pablobarron7/SmartBat_Capstone_2022/MCU Design/PCBTest.png

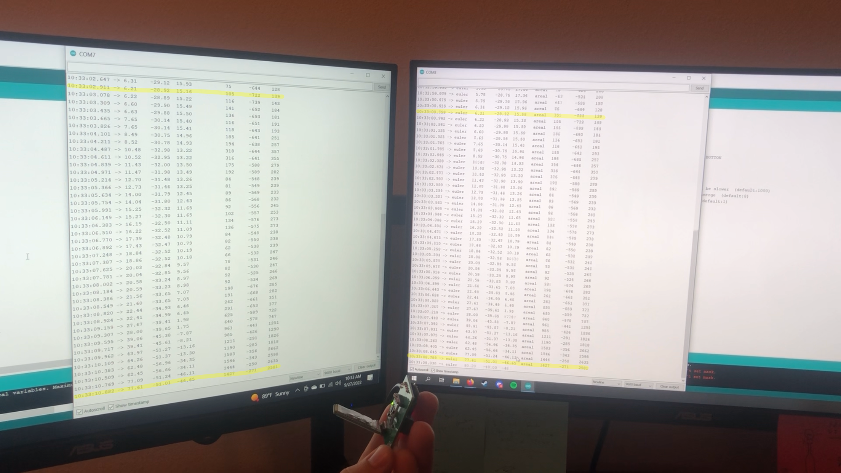
MCU Design/PCBTest.png
