pablobarron7/SmartBat_Capstone_2022/ML_EC2_Output/location3output.jpg

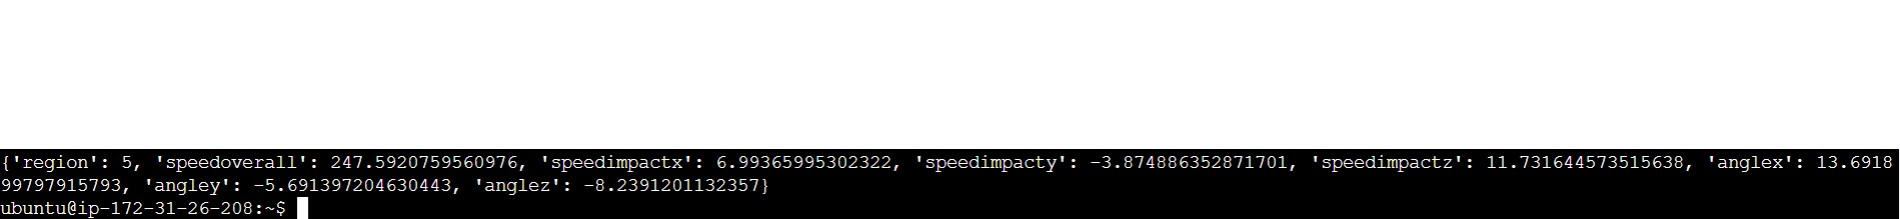
ML_EC2_Output/location3output.jpg
