pablobarron7/SmartBat_Capstone_2022/Bluetooth Validation/BTDistanceTest.PNG

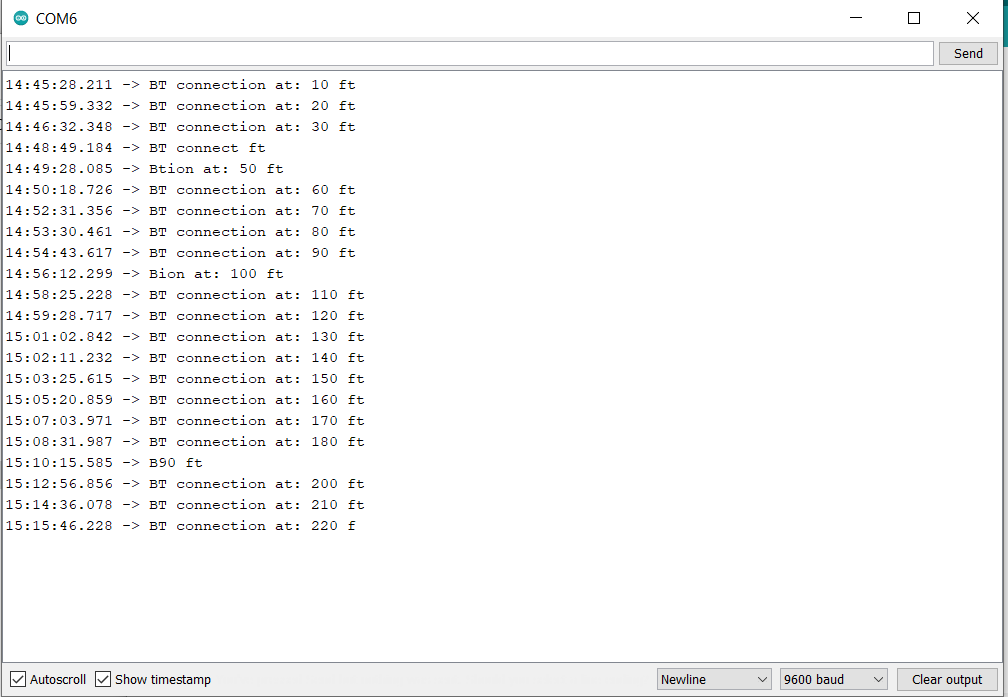
Bluetooth Validation/BTDistanceTest.PNG
