pablobarron7/SmartBat_Capstone_2022/Bluetooth Validation/Orignal Test/AppSideBTTest.PNG

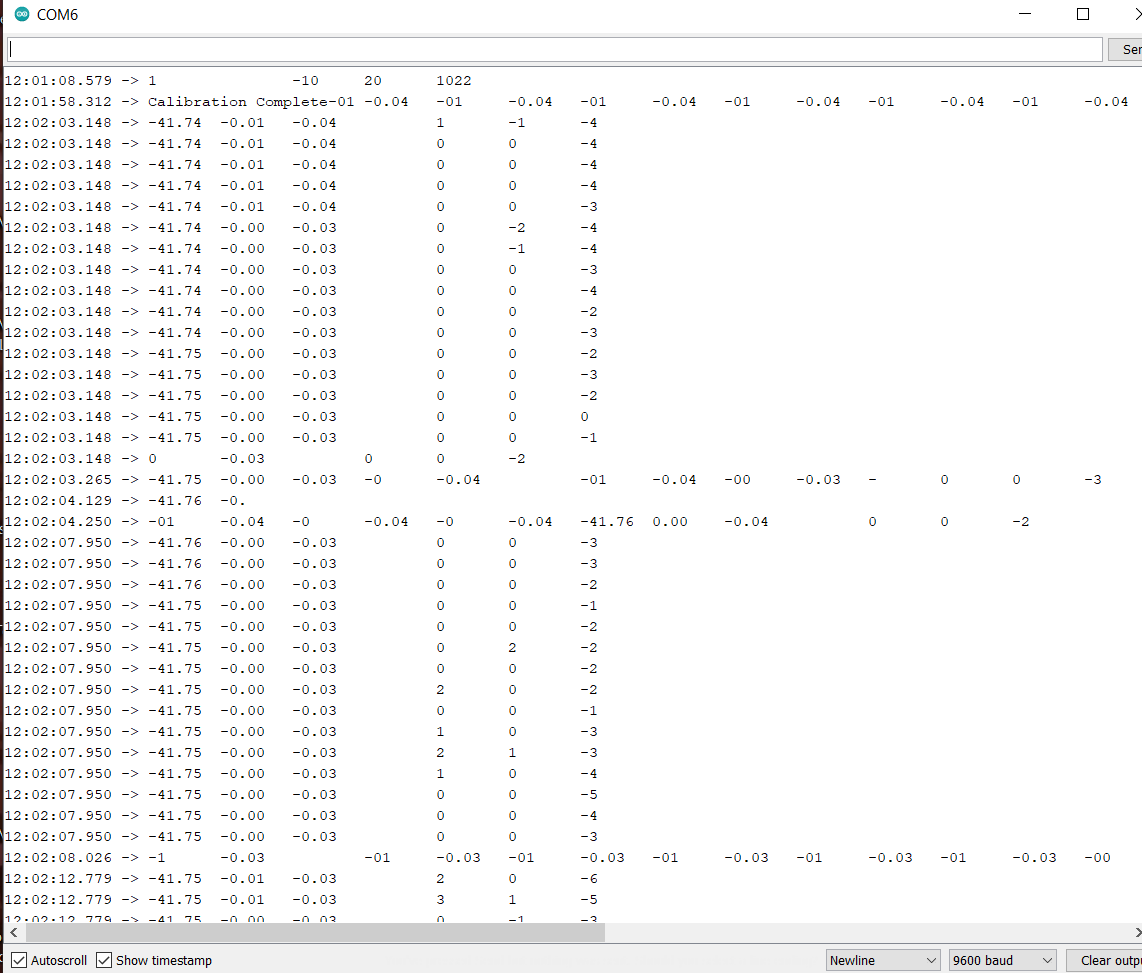
Bluetooth Validation/Orignal Test/AppSideBTTest.PNG
