pablobarron7/SmartBat_Capstone_2022/IMU Validation Plots/AccelerationMagPlot.png

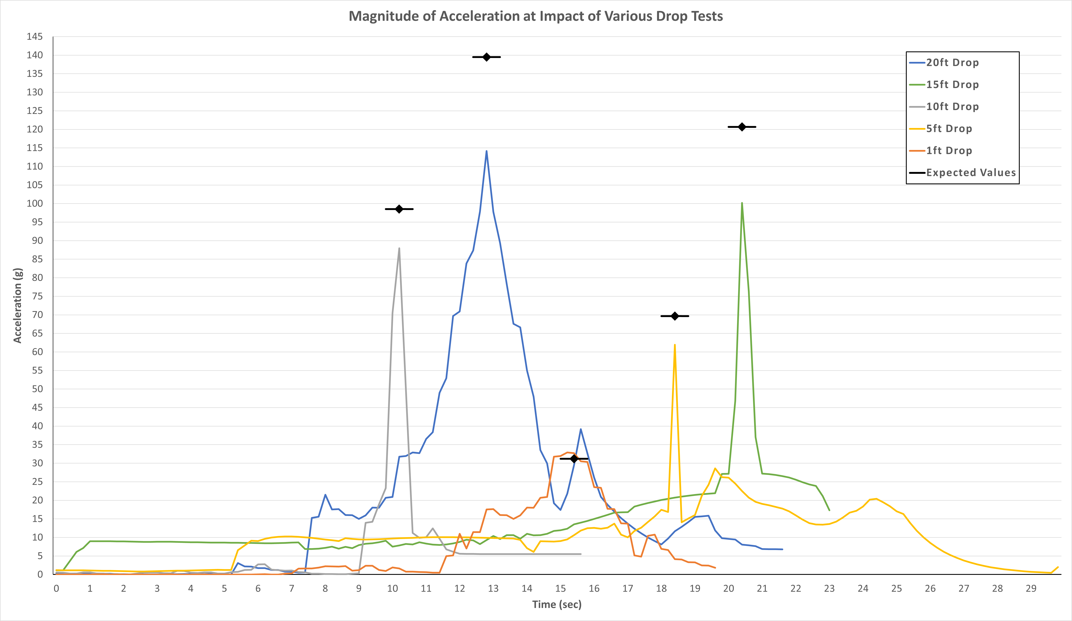
IMU Validation Plots/AccelerationMagPlot.png
