pablobarron7/SmartBat_Capstone_2022/IMU Validation Plots/GyroXAxis0to90.png

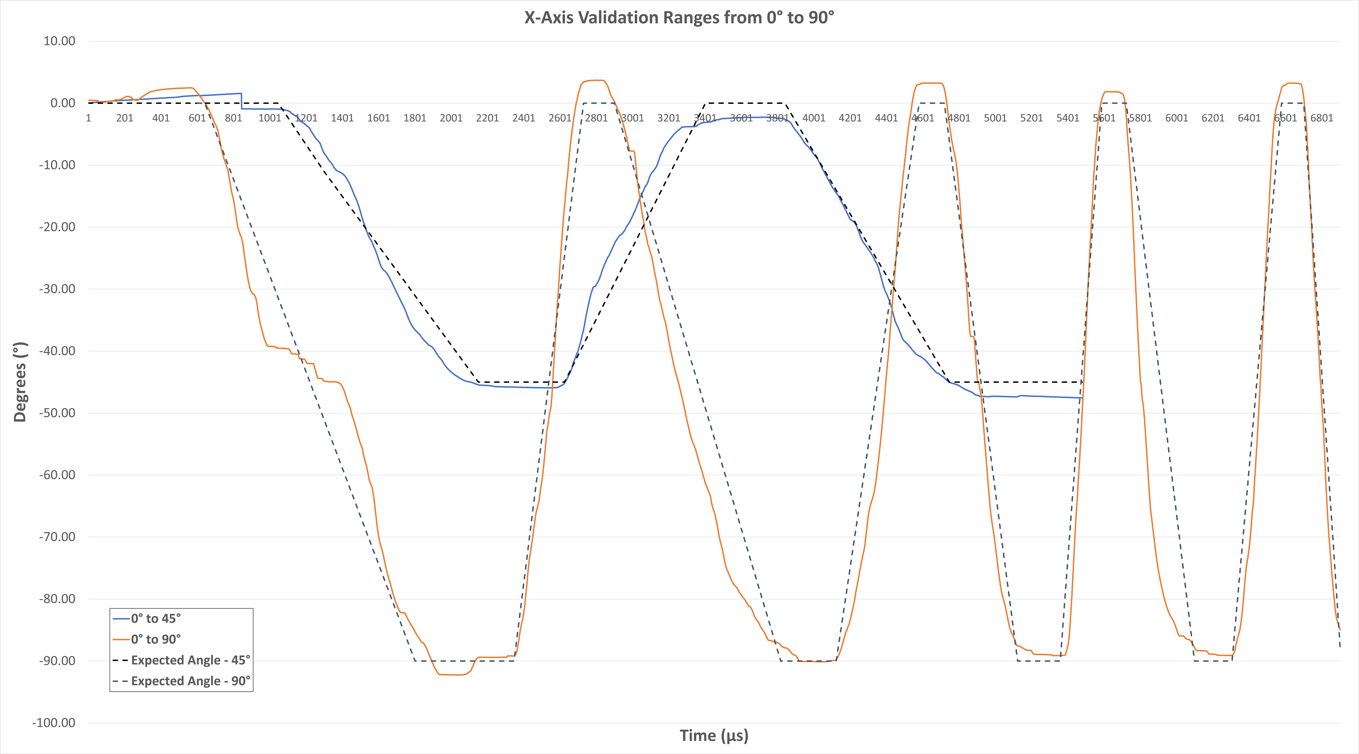
IMU Validation Plots/GyroXAxis0to90.png
