pablobarron7/SmartBat_Capstone_2022/IMU Validation Plots/GyroXAxis135to180.png

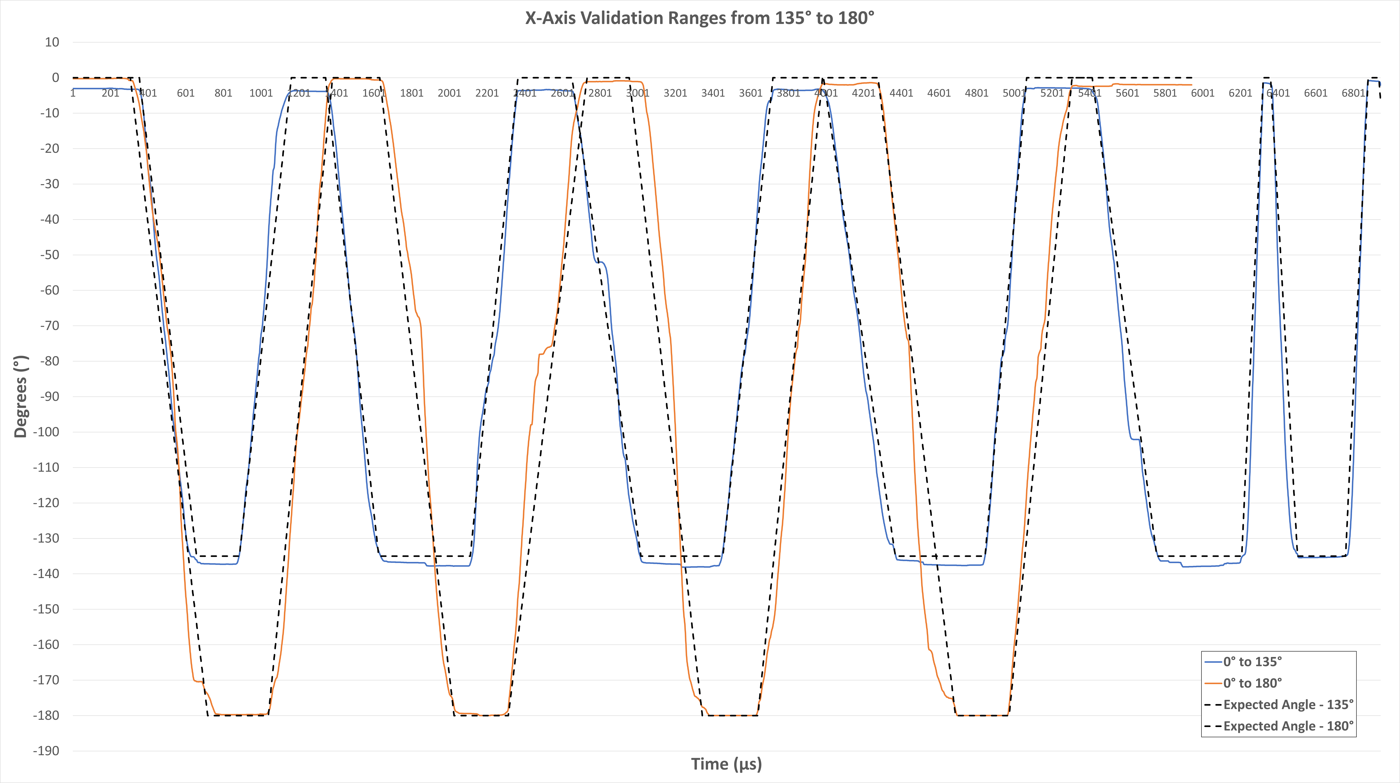
IMU Validation Plots/GyroXAxis135to180.png
