pablobarron7/SmartBat_Capstone_2022/IMU Validation Plots/GyroXAxis215to270.png

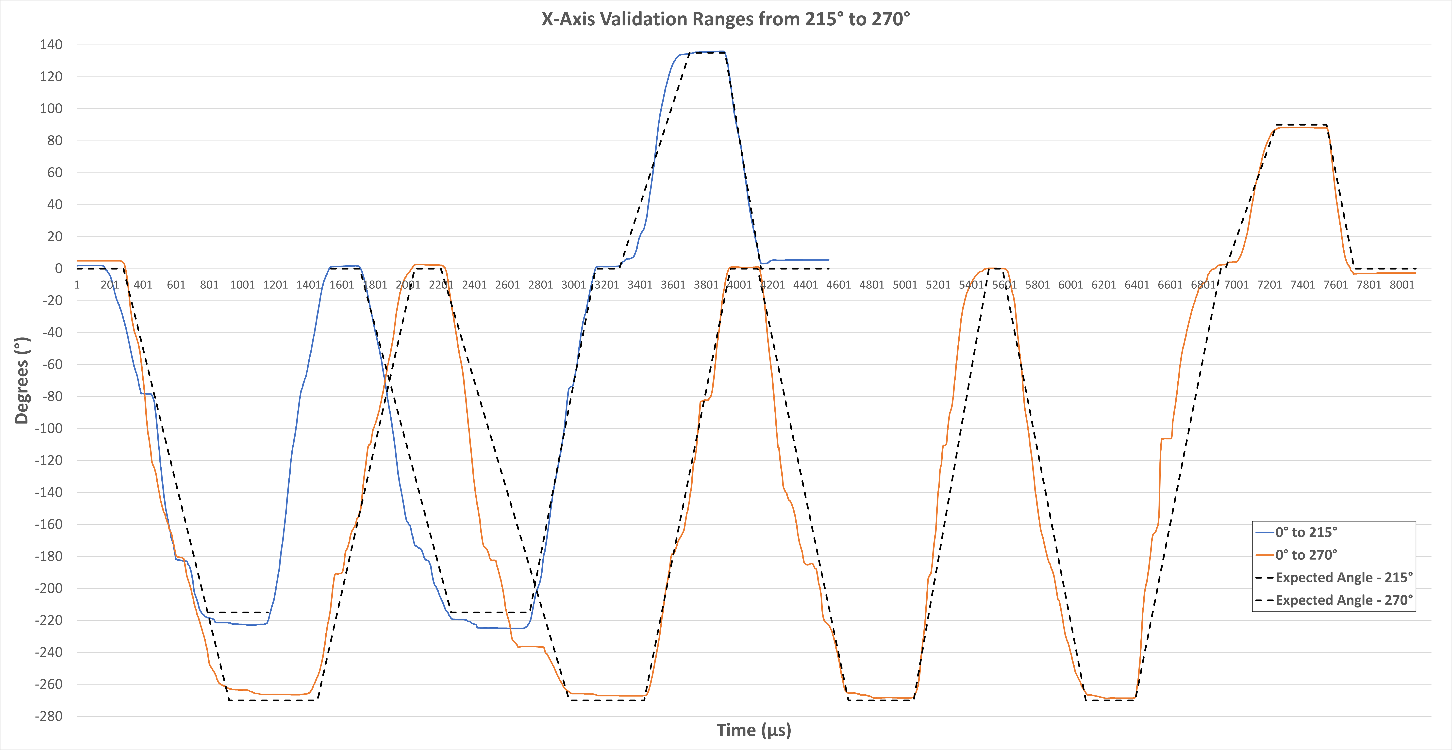
IMU Validation Plots/GyroXAxis215to270.png
