pablobarron7/SmartBat_Capstone_2022/IMU Validation Plots/GyroXAxis315to360.png

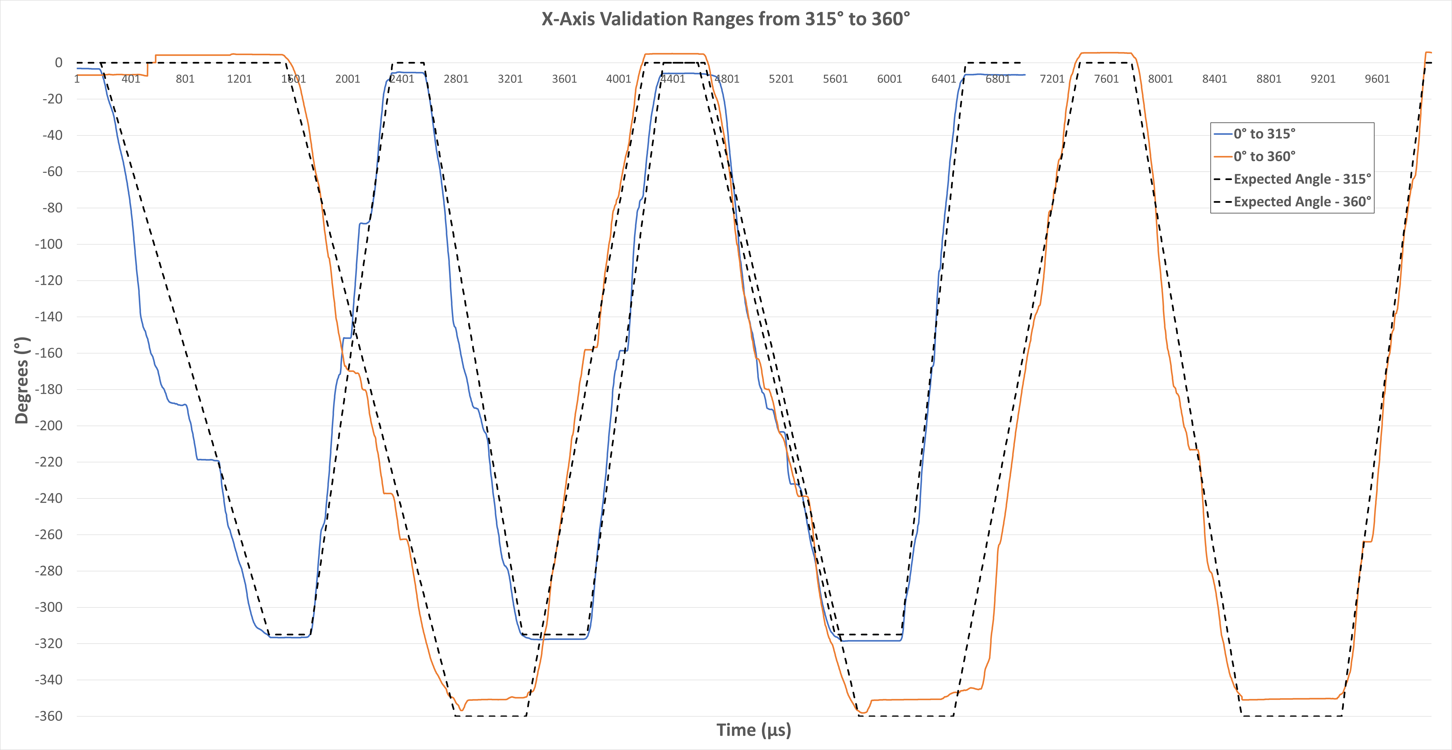
IMU Validation Plots/GyroXAxis315to360.png
