pablobarron7/SmartBat_Capstone_2022/IMU Validation Plots/GyroYAxis0to180.png

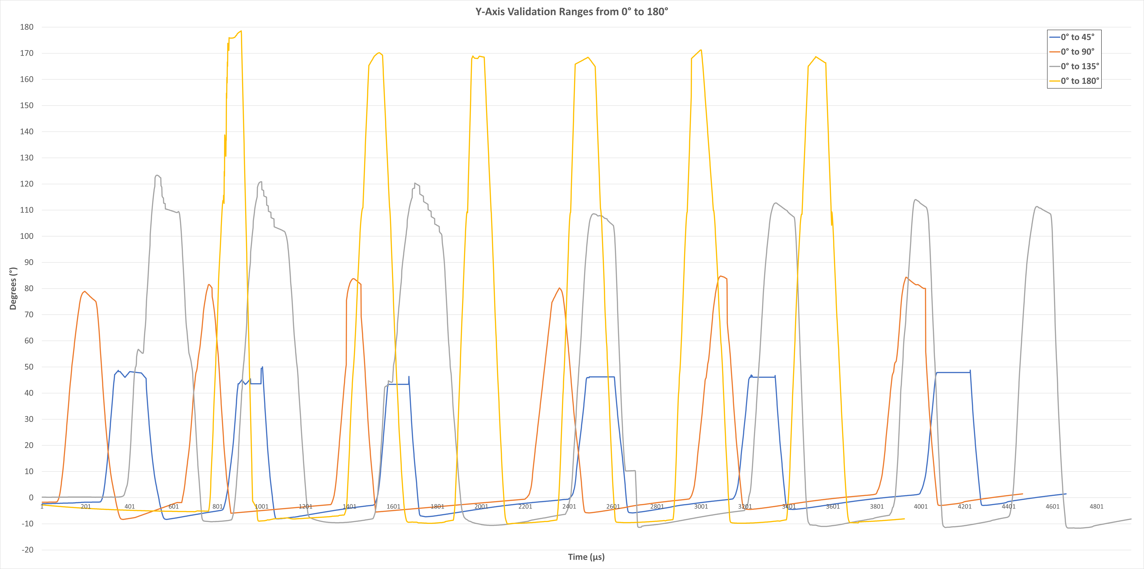
IMU Validation Plots/GyroYAxis0to180.png
