pablobarron7/SmartBat_Capstone_2022/IMU Validation Plots/GyroZAxis0to360.png

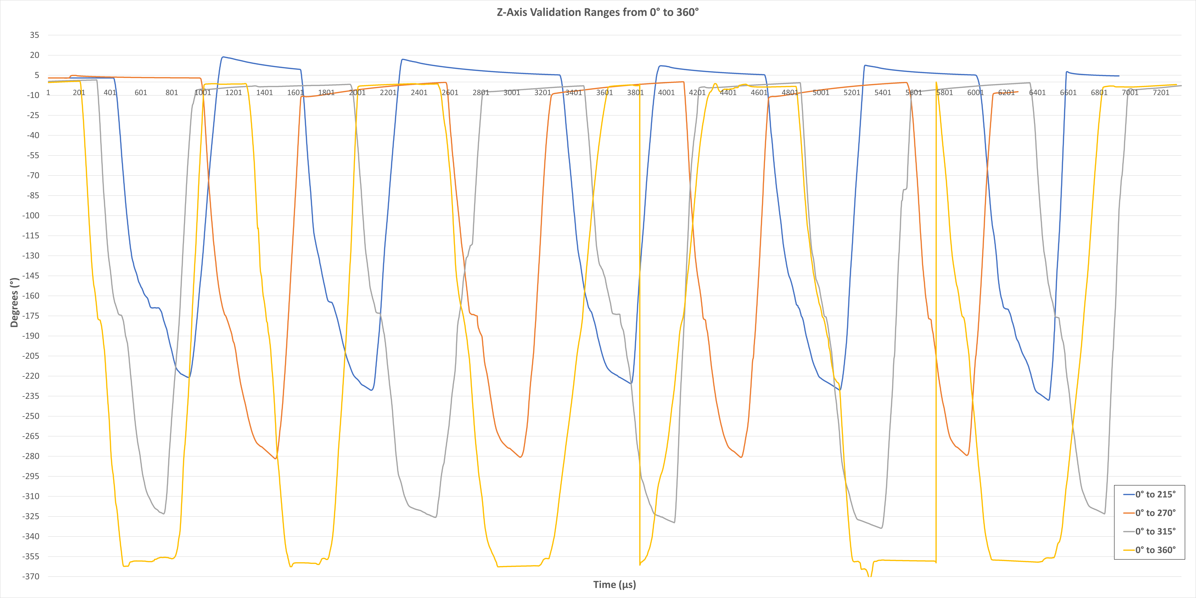
IMU Validation Plots/GyroZAxis0to360.png
