pablobarron7/SmartBat_Capstone_2022/IMU Validation Plots/GyroZAxis135to180.png

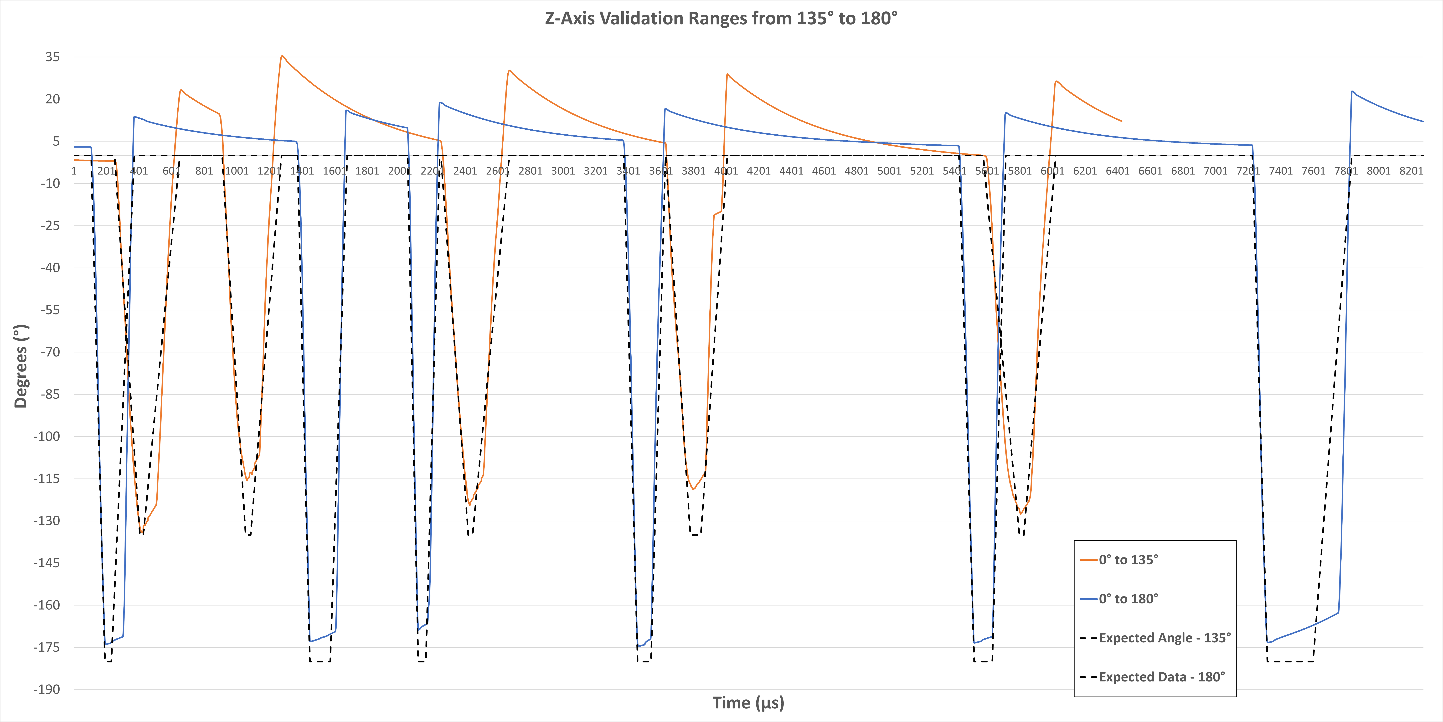
IMU Validation Plots/GyroZAxis135to180.png
