pablobarron7/SmartBat_Capstone_2022/IMU Validation Plots/GyroZAxis215to270.png

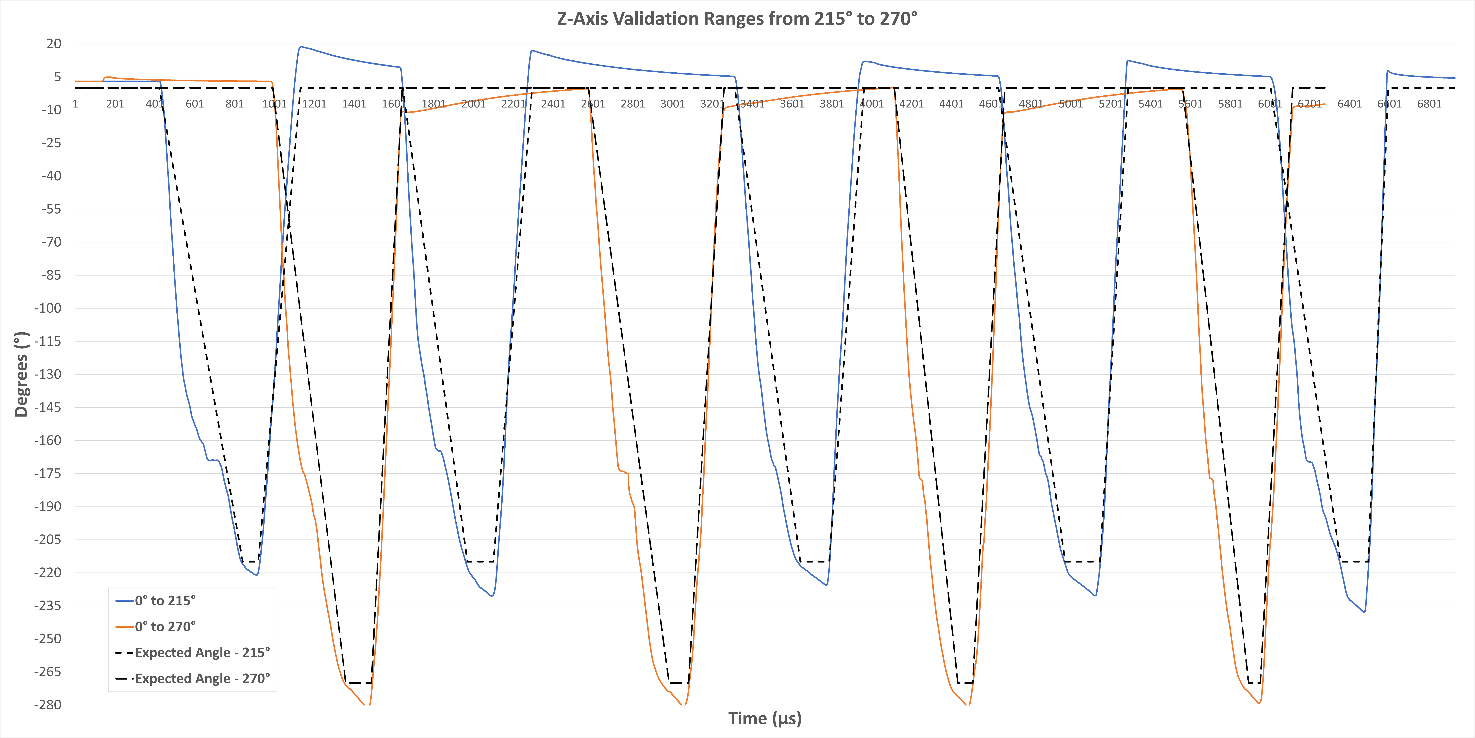
IMU Validation Plots/GyroZAxis215to270.png
