pablobarron7/SmartBat_Capstone_2022/ML Validation/ML Model Plots/afterdemo9.PNG

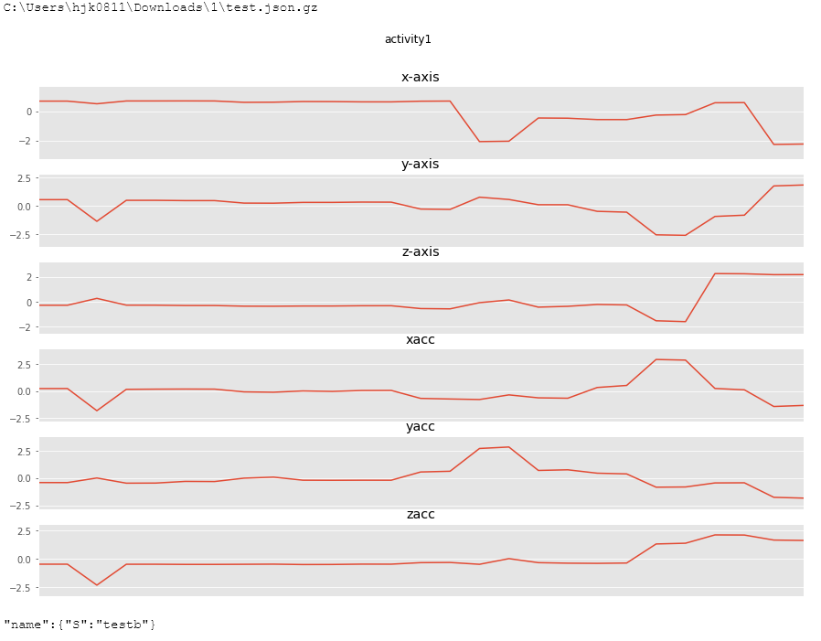
ML Validation/ML Model Plots/afterdemo9.PNG
