pablobarron7/SmartBat_Capstone_2022/ML Validation/ML Model Plots/thurshit1.PNG

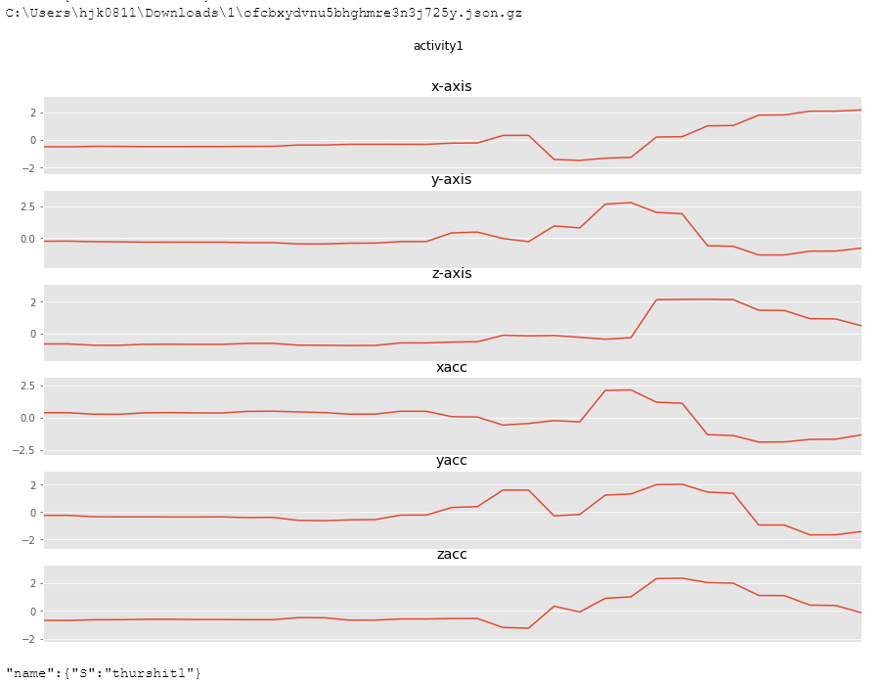
ML Validation/ML Model Plots/thurshit1.PNG
