pablobarron7/SmartBat_Capstone_2022/ML Validation/ML Model Plots/thurshit10.PNG

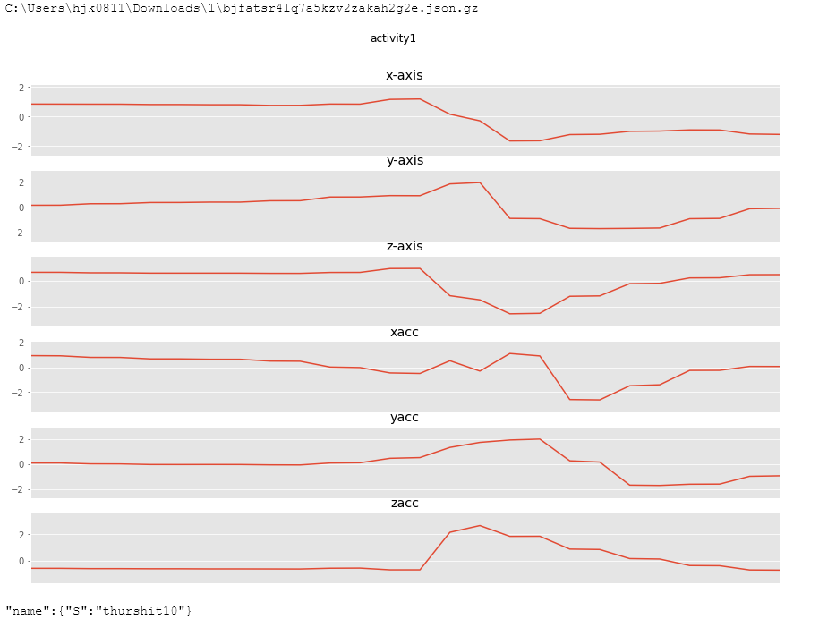
ML Validation/ML Model Plots/thurshit10.PNG
