pablobarron7/SmartBat_Capstone_2022/ML Validation/ML Model Plots/tueshit12a.png

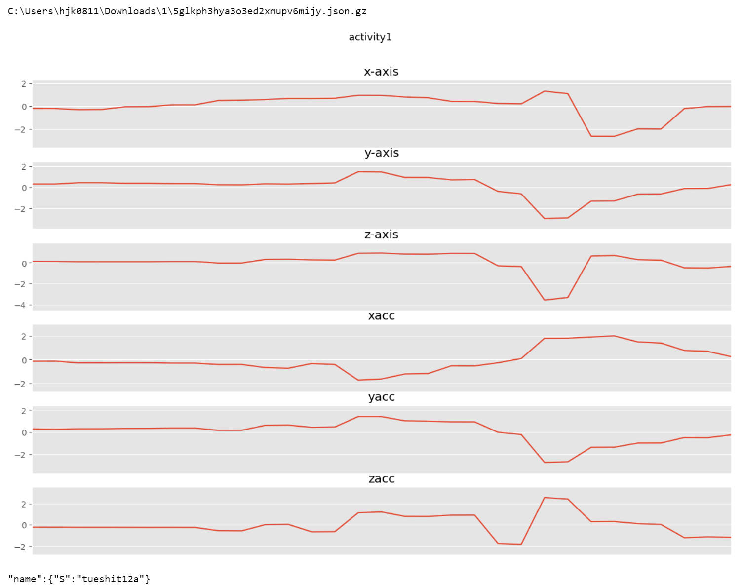
ML Validation/ML Model Plots/tueshit12a.png
