pablobarron7/SmartBat_Capstone_2022/ML Validation/ML Model Plots/wedhit11.png

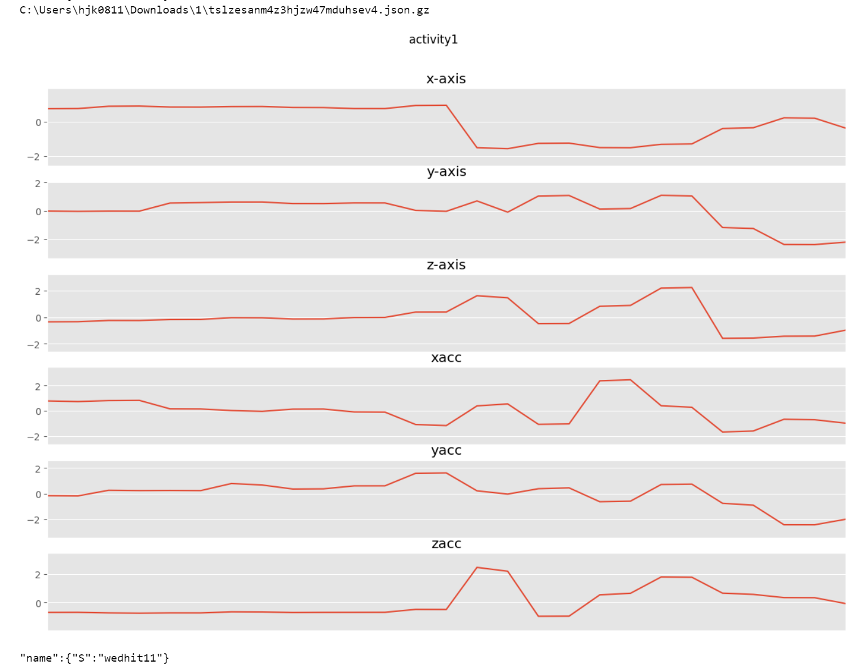
ML Validation/ML Model Plots/wedhit11.png
